m0Ssss/hybrid_charge_controller/energymeadow.kicad_sch

## KiCad design energymeadow.kicad_sch (2024-06-17)

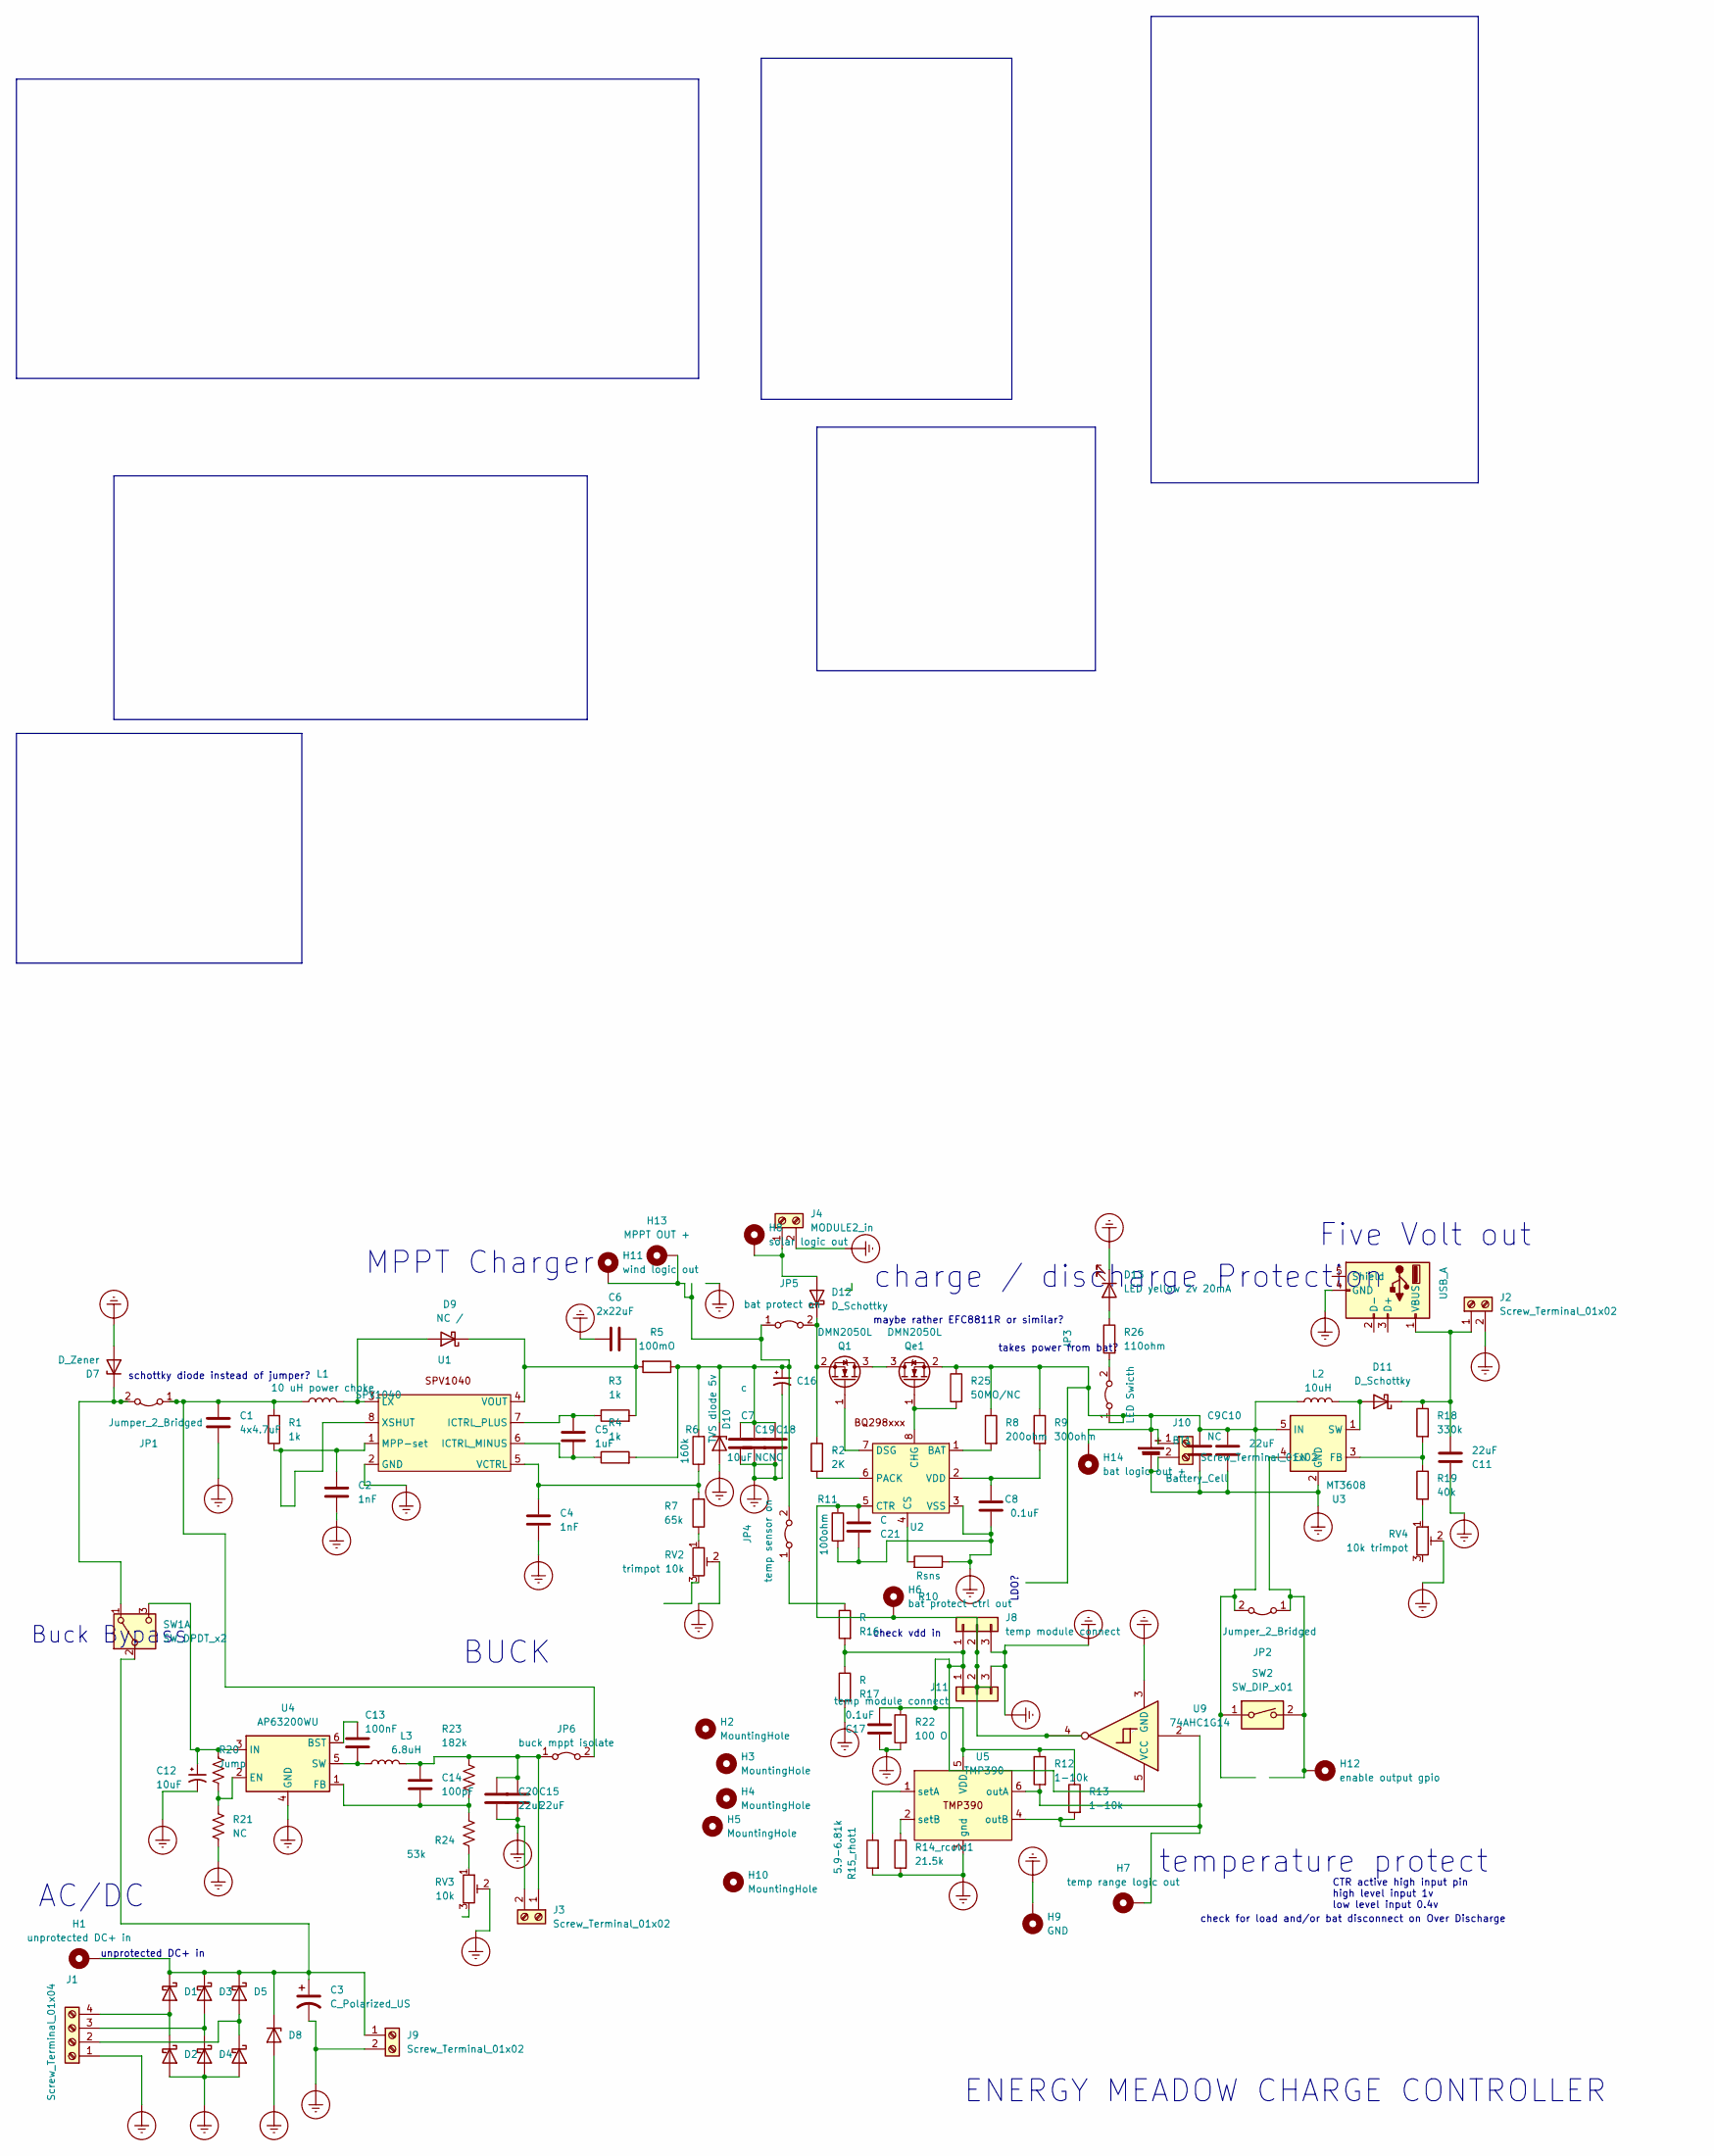
[picture p2: schematic energymeadow.kicad_sch]

Parts:
5VOUT1: USB_A; USB_A_TE_292303-7_Horizontal
BT1: Battery_Cell; BatteryHolder_Keystone_1042_1x18650
C1: 4x4.7uF; C_0805_2012Metric_Pad1.18x1.45mm_HandSolder
C2, C4: 1nF; C_0805_2012Metric_Pad1.18x1.45mm_HandSolder
C3: C_Polarized_US; CP_Radial_D5.0mm_P2.50mm
C5: 1uF; C_0805_2012Metric_Pad1.18x1.45mm_HandSolder
C6: 2x22uF; C_0805_2012Metric_Pad1.18x1.45mm_HandSolder
C7, C9, C18: NC; C_0805_2012Metric_Pad1.18x1.45mm_HandSolder
C8, C17: 0.1uF; C_0805_2012Metric_Pad1.18x1.45mm_HandSolder
C10, C11: 22uF; C_0805_2012Metric_Pad1.18x1.45mm_HandSolder
C12: 10uF; CP_Radial_D4.0mm_P1.50mm
C13: 100nF; C_0805_2012Metric_Pad1.18x1.45mm_HandSolder
C14: 100pF; C_0805_2012Metric_Pad1.18x1.45mm_HandSolder
C15, C20: 22uF; CP_Radial_D4.0mm_P1.50mm
C16: c; CP_Radial_D4.0mm_P1.50mm
C19: 10uF; C_0805_2012Metric_Pad1.18x1.45mm_HandSolder
C21: C; C_0805_2012Metric_Pad1.18x1.45mm_HandSolder
D1, D2, D3, D4, D5, D6: Schottky 40V 3A SB340-E3/73; D_5W_P12.70mm_Horizontal
D7: D_Zener; D_Powermite2_AK
D8: Zener 30V 5W 1N5363B-TP; D_Powermite2_AK
D9: NC /; D_0805_2012Metric_Pad1.15x1.40mm_HandSolder
D10: TVS diode 5v; D_Powermite_AK
D11, D12: D_Schottky; D_0805_2012Metric_Pad1.15x1.40mm_HandSolder
D13: LED yellow 2v 20mA; LED_0805_2012Metric_Pad1.15x1.40mm_HandSolder
H1: unprotected DC+ in; TestPoint_THTPad_D2.0mm_Drill1.0mm
H2, H3, H4, H5: MountingHole; MountingHole_2.7mm_M2.5_DIN965
H6: bat protect ctrl out; TestPoint_THTPad_1.0x1.0mm_Drill0.5mm
H7: temp range logic out; TestPoint_THTPad_1.0x1.0mm_Drill0.5mm
H8: solar logic out; TestPoint_THTPad_1.0x1.0mm_Drill0.5mm
H9: GND; TestPoint_THTPad_2.0x2.0mm_Drill1.0mm
H10: MountingHole; drillhole_0_5
H11: wind logic out; TestPoint_THTPad_1.0x1.0mm_Drill0.5mm
H12: enable output gpio; TestPoint_THTPad_1.0x1.0mm_Drill0.5mm
H13: MPPT OUT +; TestPoint_THTPad_D2.0mm_Drill1.0mm
H14: bat logic out +; TestPoint_THTPad_1.0x1.0mm_Drill0.5mm
J1: Screw_Terminal_01x04; TerminalBlock_MetzConnect_Type055_RT01504HDWU_1x04_P5.00mm_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
J2, J3, J9: Screw_Terminal_01x02; TerminalBlock_MetzConnect_Type059_RT06302HBWC_1x02_P3.50mm_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
J4: MODULE2_in; TerminalBlock_MetzConnect_Type059_RT06302HBWC_1x02_P3.50mm_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
J8, J11: temp module connect; PinHeader_1x03_P2.00mm_Vertical
J10: Screw_Terminal_01x02; JST_PH_S2B-PH-K_1x02_P2.00mm_Horizontal
JP1, JP2: Jumper_2_Bridged; TestPoint_2Pads_Pitch2.54mm_Drill0.8mm
JP3: LED Swicth; TestPoint_2Pads_Pitch2.54mm_Drill0.8mm
JP4: temp sensor on; TestPoint_2Pads_Pitch2.54mm_Drill0.8mm
JP5: bat protect on; TestPoint_2Pads_Pitch2.54mm_Drill0.8mm
JP6: buck mppt isolate; TestPoint_2Pads_Pitch2.54mm_Drill0.8mm
L1: 10 uH power choke; L_6.3x6.3_H3
L2: 10uH; L_6.3x6.3_H3
L3: 6.8uH; L_6.3x6.3_H3
Q1: DMN2050L; SOT-23
Qe1: DMN2050L; SOT-23
R1, R3, R4: 1k; R_0805_2012Metric_Pad1.20x1.40mm_HandSolder
R2: 2K; R_0805_2012Metric_Pad1.20x1.40mm_HandSolder
R5: 100mO; R_0805_2012Metric_Pad1.20x1.40mm_HandSolder
R6: 160k; R_0805_2012Metric_Pad1.20x1.40mm_HandSolder
R7: 65k; R_0805_2012Metric_Pad1.20x1.40mm_HandSolder
R8: 200ohm; R_0805_2012Metric_Pad1.20x1.40mm_HandSolder
R9: 300ohm; R_0805_2012Metric_Pad1.20x1.40mm_HandSolder
R10: Rsns; R_0805_2012Metric_Pad1.20x1.40mm_HandSolder
R11: 100ohm; R_0805_2012Metric_Pad1.20x1.40mm_HandSolder
R12, R13: 1-10k; R_0805_2012Metric_Pad1.20x1.40mm_HandSolder
R14_rcold1: 21.5k; R_0805_2012Metric_Pad1.20x1.40mm_HandSolder
R15_rhot1: 5.9-6.81k; R_0805_2012Metric_Pad1.20x1.40mm_HandSolder
R16, R17: R; R_0805_2012Metric_Pad1.20x1.40mm_HandSolder
R18: 330k; R_0805_2012Metric_Pad1.20x1.40mm_HandSolder
R19: 40k; R_0805_2012Metric_Pad1.20x1.40mm_HandSolder
R20: Jump; R_0805_2012Metric_Pad1.20x1.40mm_HandSolder
R21: NC; R_0805_2012Metric_Pad1.20x1.40mm_HandSolder
R22: 100 O; R_0805_2012Metric_Pad1.20x1.40mm_HandSolder
R23: 182k; R_0805_2012Metric_Pad1.20x1.40mm_HandSolder
R24: 53k; R_0805_2012Metric_Pad1.20x1.40mm_HandSolder
R25: 50MO/NC; R_0805_2012Metric_Pad1.20x1.40mm_HandSolder
R26: 110ohm; R_0805_2012Metric_Pad1.20x1.40mm_HandSolder
RV2: trimpot 10k; Potentiometer_ACP_CA6-VSMD_Vertical
RV3: 10k; Potentiometer_ACP_CA6-VSMD_Vertical
RV4: 10k trimpot; Potentiometer_ACP_CA6-VSMD_Vertical
SW1: SW_DPDT_x2; SWITCH_SLIDE
SW2: SW_DIP_x01; SWITCH_SLIDE
U1: SPV1040; TSSOP-8_3x3mm_P0.65mm
U2: Texas_X2QFN-8_1.5x1.5mm
U3: MT3608; SOT-23-6
U4: AP63200WU; TSOT-23-6
U5: TMP390; SOT-563
U9: 74AHC1G14; SOT-353_SC-70-5_Handsoldering

Connections:
Earth_Protective: 5VOUT1.4 (GND), BT1.2 (-), C1.2, C2.2, C3.2, C4.2, C6.1, C7.2, C8.1, C9.1, C10.1, C11.1, C12.2, C15.2, C16.2, C17.1, C18.2, C19.2, C20.2, C21.1, D2.2 (A), D4.2 (A), D6.2 (A), D7.2 (A), D8.2 (A), D10.2 (A), D13.1 (K), H9.1, J1.1, J2.2, J3.2, J4.2, J8.3, J9.2, J10.2, J11.3, R10.1, R11.2, R14_rcold1.2, R15_rhot1.2, R17.2, R21.2, R22.2, RV2.2, RV3.2, RV4.2, U1.2 (GND), U2.3 (VSS), U3.2 (GND), U4.4 (GND), U5.3 (gnd), U9.3 (GND)
unnamed: 5VOUT1.1 (VBUS), C11.2, D11.1 (K), J2.1, R18.1
unnamed: BT1.1 (+), C9.2, C10.2, H14.1, J10.1, JP2.2 (B), JP3.1 (A), L2.1, Qe1.2 (S), R8.1, R9.1, R25.1, SW2.1, U3.5 (IN)
unnamed: C1.1, JP1.1 (A), JP6.2 (B), L1.1, R1.2
unnamed: C2.1, R1.1, U1.1 (MPP-set), U1.8 (XSHUT)
unnamed: C3.1, D1.1 (K), D3.1 (K), D5.1 (K), D8.1 (K), H1.1, J9.1, SW1.2 (B)
unnamed: C4.1, R6.1, R7.2, U1.5 (VCTRL)
unnamed: C5.1, R3.1, U1.7 (ICTRL_PLUS)
unnamed: C5.2, R4.1, U1.6 (ICTRL_MINUS)
unnamed: C6.2, D9.1 (K), R3.2, R5.2, U1.4 (VOUT)
unnamed: C8.2, R9.2, U2.2 (VDD)
unnamed: C12.1, R20.1, SW1.3 (C), U4.3 (IN)
unnamed: C13.1, U4.6 (BST)
unnamed: C13.2, L3.1, U4.5 (SW)
unnamed: C14.1, C15.1, C20.1, J3.1, JP6.1 (A), L3.2, R23.1
unnamed: C14.2, R23.2, R24.1, U4.1 (FB)
unnamed: C7.1, C16.1, C18.1, C19.1, D10.1 (K), H11.1, H13.1, JP4.2 (B), JP5.1 (A), R4.2, R5.1, R6.2
unnamed: C17.2, J8.1, J11.1, R12.1, R13.1, R16.2, R17.1, R22.1, U5.5 (VDD), U9.5 (VCC)
unnamed: C21.2, H6.1, J8.2, J11.2, R11.1, U2.5 (CTR), U9.4
unnamed: D1.2 (A), D2.1 (K), J1.4
unnamed: D3.2 (A), D4.1 (K), J1.3
unnamed: D5.2 (A), D6.1 (K), J1.2
unnamed: D7.1 (K), JP1.2 (B), SW1.1 (A)
unnamed: D9.2 (A), L1.2, U1.3 (LX)
unnamed: D11.2 (A), L2.2, U3.1 (SW)
unnamed: D12.1 (K), JP5.2 (B), Q1.2 (S), R2.1
unnamed: D12.2 (A), H8.1, J4.1
unnamed: D13.2 (A), R26.1
unnamed: H7.1, R12.2, R13.2, U5.4 (outB), U5.6 (outA), U9.2
unnamed: H12.1, JP2.1 (A), SW2.2, U3.4 (EN)
unnamed: JP3.2 (B), R26.2
unnamed: JP4.1 (A), R16.1
unnamed: Q1.1 (G), U2.7 (DSG)
unnamed: Q1.3 (D), Qe1.3 (D)
unnamed: Qe1.1 (G), R25.2, U2.8 (CHG)
unnamed: R2.2, U2.6 (PACK)
unnamed: R7.1, RV2.1
unnamed: R8.2, U2.1 (BAT)
unnamed: R10.2, U2.4 (CS)
unnamed: R14_rcold1.1, U5.2 (setB)
unnamed: R15_rhot1.1, U5.1 (setA)
unnamed: R18.2, R19.1, U3.3 (FB)
unnamed: R19.2, RV4.1
unnamed: R20.2, R21.1, U4.2 (EN)
unnamed: R24.2, RV3.1

Notes on the sheet:
AC/DC
ENERGY MEADOW CHARGE CONTROLLER
charge / discharge Protection
unprotected DC+ in
Buck Bypass
check vdd in
LDO?
CTR active high input pin high level input 1v low level input 0.4v
MPPT Charger
maybe rather EFC8811R or similar?
takes power from bat?
Five Volt out
check for load and/or bat disconnect on Over Discharge
BUCK
schottky diode instead of jumper?
temperature protect
