m0Ssss/hybrid_charge_controller/wind charge controller.kicad_sch

## KiCad design wind charge controller.kicad_sch (2024-03-23)

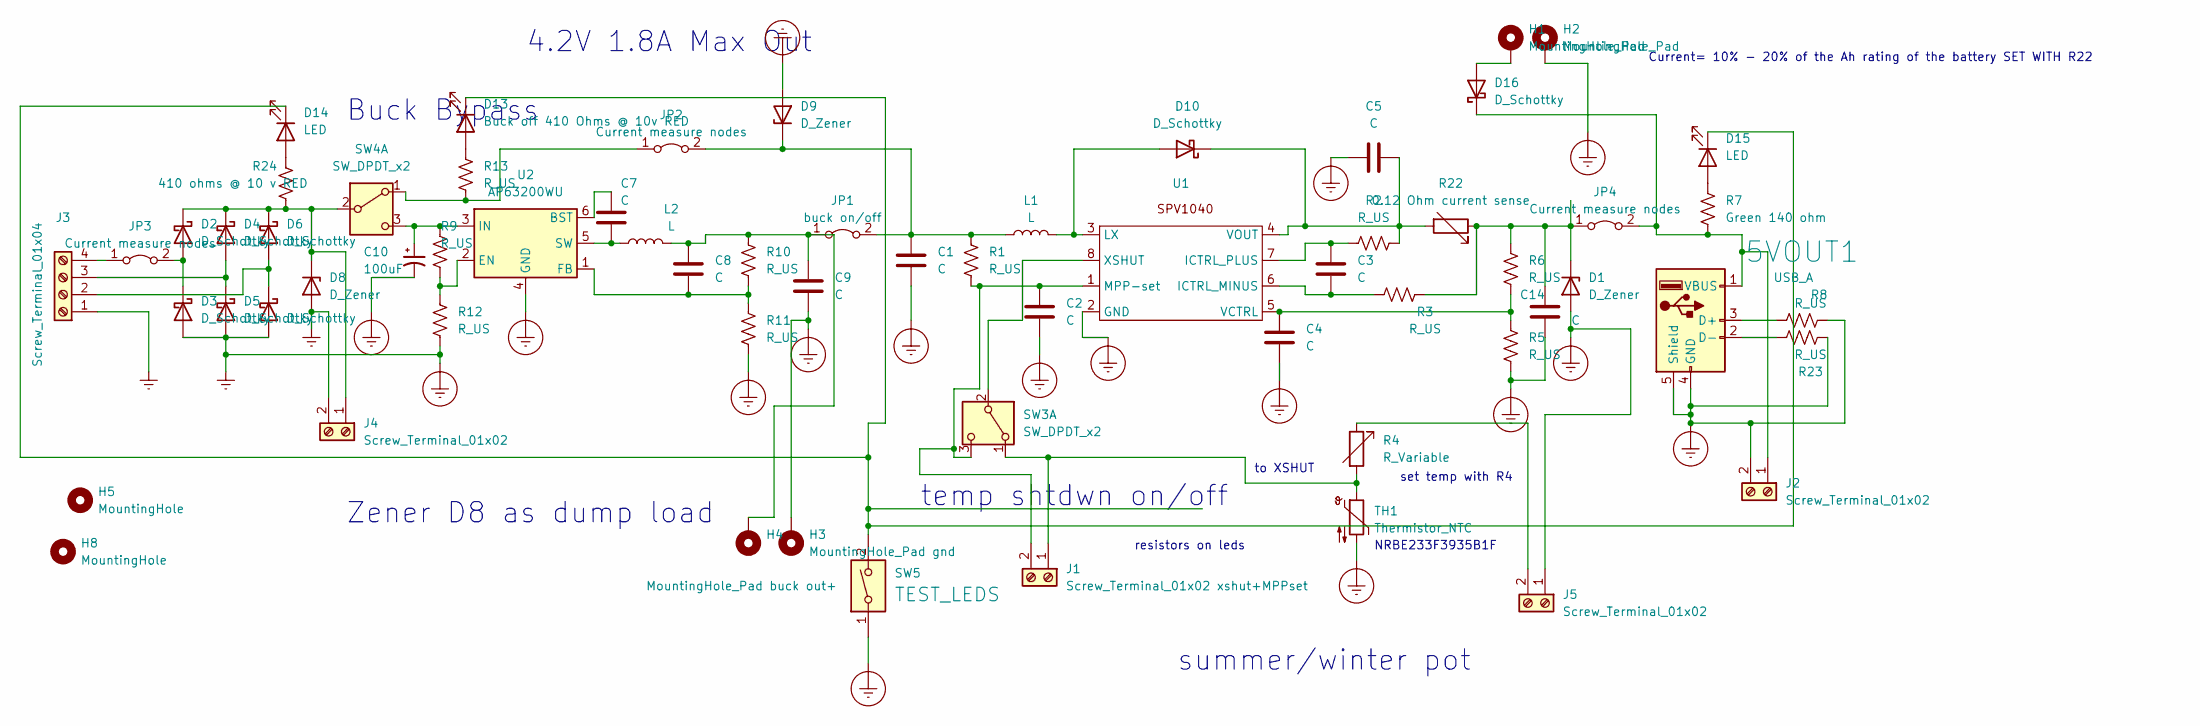
[picture p3: schematic wind charge controller.kicad_sch]

Parts:
5VOUT1: USB_A; USB_A_TE_292303-7_Horizontal
C1, C2, C3, C4, C5, C7, C8, C9, C14: C; CP_Radial_D4.0mm_P1.50mm
C10: 100uF; CP_Radial_D4.0mm_P1.50mm
D1, D8, D9: D_Zener; D_5W_P12.70mm_Horizontal
D2, D3, D4, D5, D6, D7, D16: D_Schottky; D_5W_P12.70mm_Horizontal
D10: D_Schottky; D_DO-15_P2.54mm_Vertical_AnodeUp
D13: Buck off 410 Ohms @ 10v RED; LED_D3.0mm
D14, D15: LED; LED_D3.0mm
H1, H2: MountingHole_Pad; MountingHole_2.2mm_M2_DIN965_Pad
H3: MountingHole_Pad gnd; MountingHole_2.2mm_M2_DIN965_Pad
H4: MountingHole_Pad buck out+; MountingHole_2.2mm_M2_DIN965_Pad
H5, H8: MountingHole; MountingHole_3.2mm_M3
J1: Screw_Terminal_01x02 xshut+MPPset; TerminalBlock_bornier-2_P5.08mm
J2, J4, J5: Screw_Terminal_01x02; TerminalBlock_bornier-2_P5.08mm
J3: Screw_Terminal_01x04; TerminalBlock_RND_205-00025_1x04_P10.00mm_Horizontal
JP1: buck on/off; TestPoint_2Pads_Pitch2.54mm_Drill0.8mm
JP2, JP3, JP4: Current measure nodes; TestPoint_2Pads_Pitch2.54mm_Drill0.8mm
L1, L2: L; L_Radial_D7.5mm_P5.00mm_Fastron_07P
R1, R2, R3, R5, R6, R8, R9, R10, R11, R12, R13, R23: R_US; R_Axial_DIN0309_L9.0mm_D3.2mm_P12.70mm_Horizontal
R4: R_Variable; Potentiometer_TT_P0915N
R7: Green 140 ohm; R_Axial_DIN0309_L9.0mm_D3.2mm_P12.70mm_Horizontal
R22: 0.12 Ohm current sense; R_Axial_DIN0309_L9.0mm_D3.2mm_P12.70mm_Horizontal
R24: 410 ohms @ 10 v RED; R_Axial_DIN0309_L9.0mm_D3.2mm_P12.70mm_Horizontal
SW3, SW4: SW_DPDT_x2; SWITCH_SLIDE
SW5: TEST_LEDS; SW_SPST_TL3342
TH1: Thermistor_NTC; CP_Radial_D4.0mm_P1.50mm
U1: TSSOP-8_4.4x3mm_P0.65mm
U2: AP63200WU; TSOT-23-6

Connections:
Earth: 5VOUT1.4 (GND), 5VOUT1.5 (Shield), C1.2, C2.2, C4.2, C5.1, C9.2, C10.2, C14.2, D1.2 (A), D3.2 (A), D5.2 (A), D7.2 (A), D8.2 (A), D9.2 (A), H2.1, H3.1, J2.2, J3.1, J4.2, J5.1, R5.1, R8.1, R11.2, R12.2, R23.1, SW5.1, TH1.2, U1.2 (GND), U2.4 (GND)
unnamed: 5VOUT1.1 (VBUS), D16.1 (K), J2.1, JP4.2 (B), R7.1
unnamed: 5VOUT1.2 (D-), R23.2
unnamed: 5VOUT1.3 (D+), R8.2
unnamed: C1.1, D9.1 (K), JP1.2 (B), JP2.2 (B), L1.1, R1.1
unnamed: C2.1, J1.2, R1.2, SW3.3 (C), U1.1 (MPP-set)
unnamed: C3.1, R2.1, U1.7 (ICTRL_PLUS)
unnamed: C3.2, R3.1, U1.6 (ICTRL_MINUS)
unnamed: C4.1, R5.2, R6.1, U1.5 (VCTRL)
unnamed: C5.2, D10.1 (K), R2.2, R22.2, U1.4 (VOUT)
unnamed: C7.1, U2.6 (BST)
unnamed: C7.2, L2.1, U2.5 (SW)
unnamed: C8.1, C9.1, H4.1, JP1.1 (A), L2.2, R10.1
unnamed: C8.2, R10.2, R11.1, U2.1 (FB)
unnamed: C10.1, R9.1, SW4.3 (C), U2.3 (IN)
unnamed: C14.1, D1.1 (K), JP4.1 (A), R3.2, R6.2, R22.1
unnamed: D2.1 (K), D4.1 (K), D6.1 (K), D8.1 (K), J4.1, R24.2, SW4.2 (B)
unnamed: D2.2 (A), D3.1 (K), JP3.2 (B)
unnamed: D4.2 (A), D5.1 (K), J3.3
unnamed: D6.2 (A), D7.1 (K), J3.2
unnamed: D10.2 (A), L1.2, U1.3 (LX)
unnamed: D13.1 (K), D14.1 (K), D15.1 (K), SW5.2
unnamed: D13.2 (A), R13.1
unnamed: D14.2 (A), R24.1
unnamed: D15.2 (A), R7.2
unnamed: D16.2 (A), H1.1
unnamed: J1.1, R4.2, SW3.1 (A), TH1.1
unnamed: J3.4, JP3.1 (A)
unnamed: J5.2, R4.1
unnamed: JP2.1 (A), R13.2, SW4.1 (A)
unnamed: R9.2, R12.1, U2.2 (EN)
unnamed: SW3.2 (B), U1.8 (XSHUT)

Notes on the sheet:
to XSHUT
Zener D8 as dump load
temp shtdwn on/off
NRBE233F3935B1F
4.2V 1.8A Max Out
set temp with R4
Current= 10% - 20% of the Ah rating of the battery SET WITH R22
summer/winter pot
Buck Bypass
resistors on leds
